fabcrowd/pokescan/design/output/cs2_motor_bracket.stl

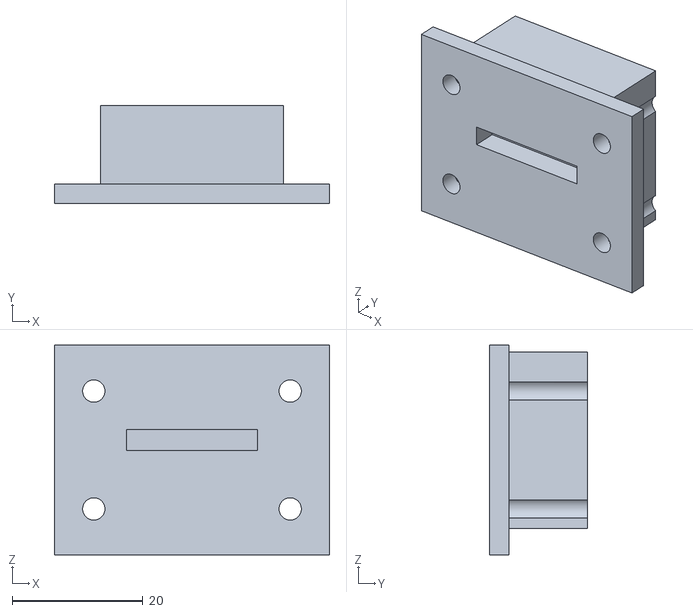
[picture p15: CAD file, 2026-06-29]
design/output/cs2_motor_bracket.stl
42.0 x 15.0 x 32.0
