fabcrowd/pokescan/design/output/cs2_separator_body.stl

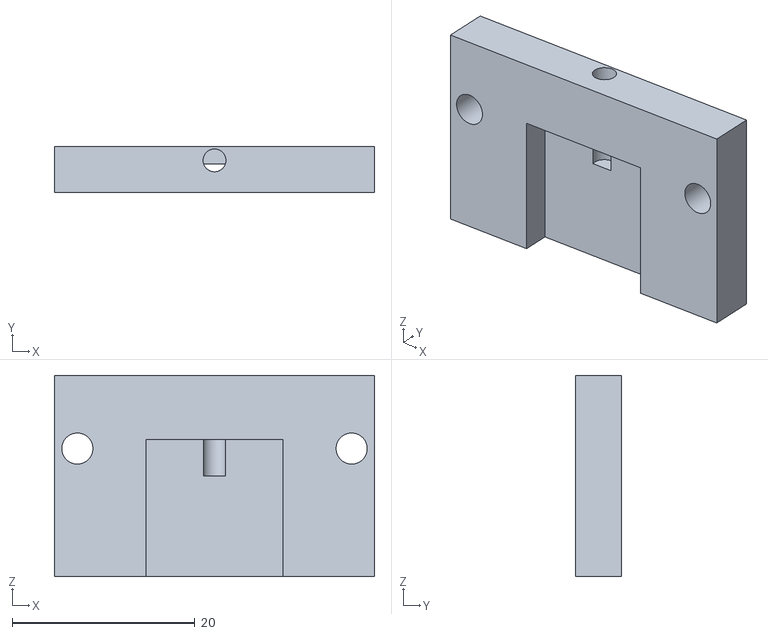
[picture p16: CAD file, 2026-06-29]
design/output/cs2_separator_body.stl
35.0 x 5.00 x 22.0
