fabcrowd/pokescan/design/output/cs2_rack_stand_fit_test.stl

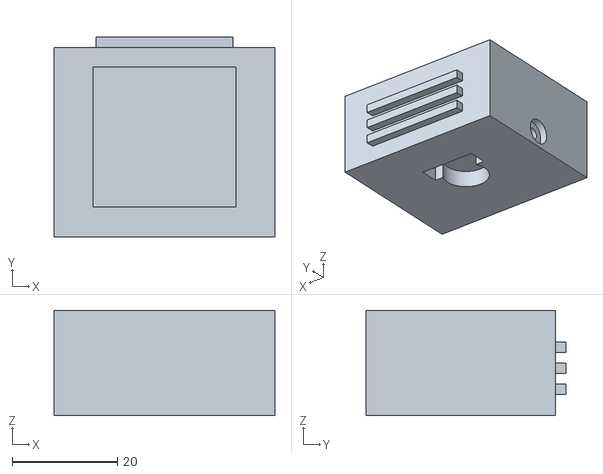
[picture p17: CAD file, 2026-06-29]
design/output/cs2_rack_stand_fit_test.stl
42.0 x 38.0 x 20.0
