fabcrowd/pokescan/design/output/cs2_push_rod.stl

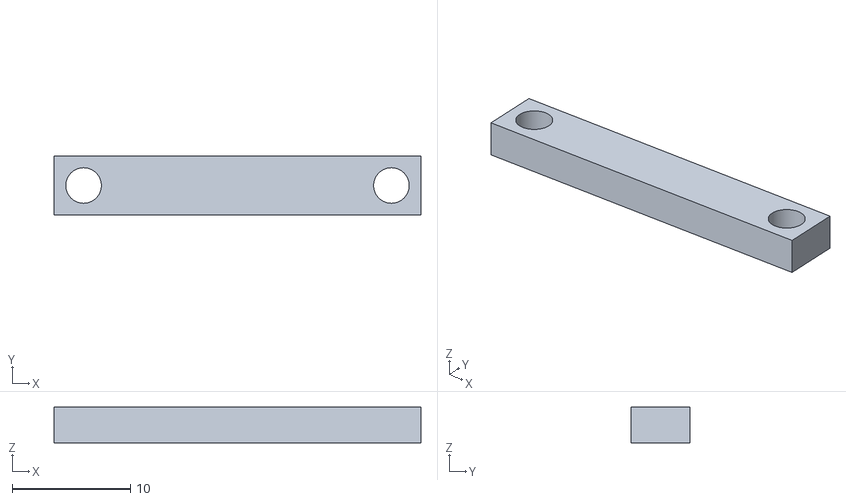
[picture p18: CAD file, 2026-06-29]
design/output/cs2_push_rod.stl
31.0 x 5.00 x 3.00
