fabcrowd/pokescan/design/output/cs2_roller_plate.stl

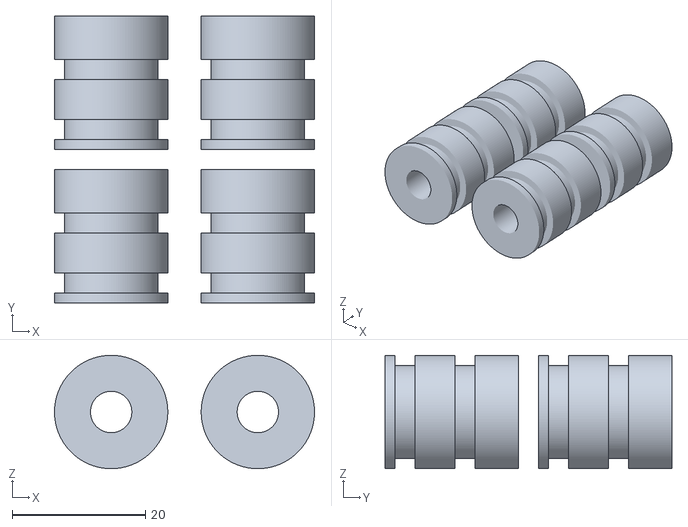
[picture p19: CAD file, 2026-06-29]
design/output/cs2_roller_plate.stl
39.0 x 43.0 x 17.0
