fabcrowd/pokescan/design/output/cs2_separator_gap_plate.stl

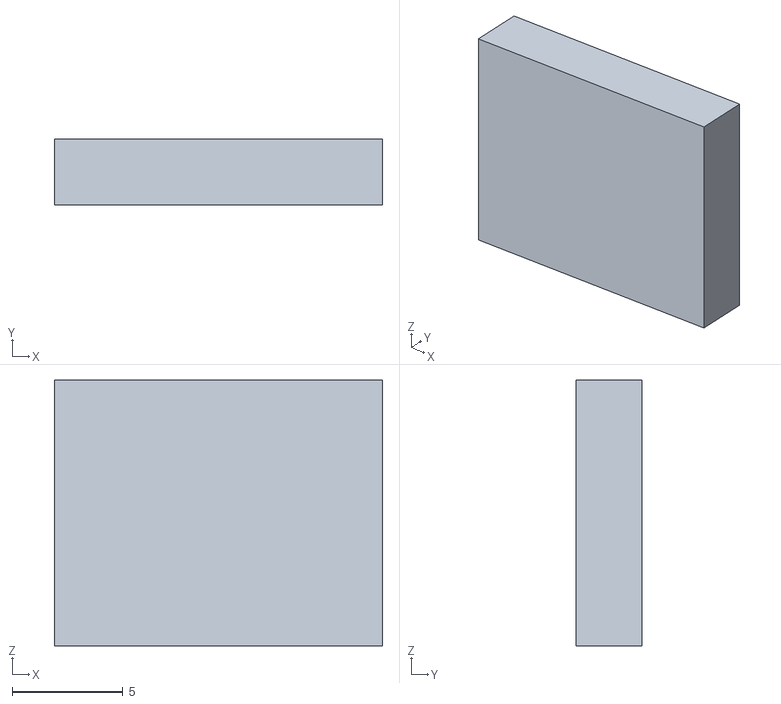
[picture p20: CAD file, 2026-06-29]
design/output/cs2_separator_gap_plate.stl
14.8 x 3.00 x 12.0
