fabcrowd/pokescan/design/output/cs2_roller.stl

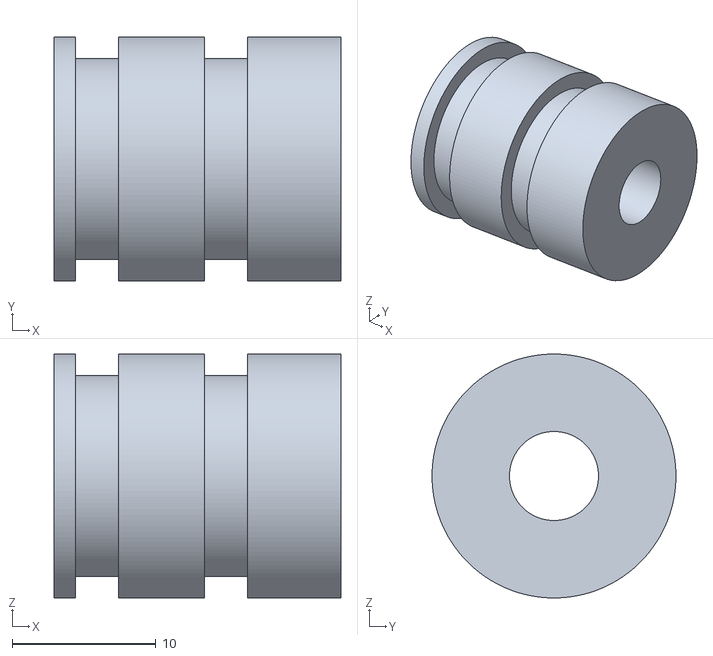
[picture p21: CAD file, 2026-06-29]
design/output/cs2_roller.stl
20.0 x 17.0 x 17.0
