fabcrowd/pokescan/design/output/cs2_rack_stand_platform.stl

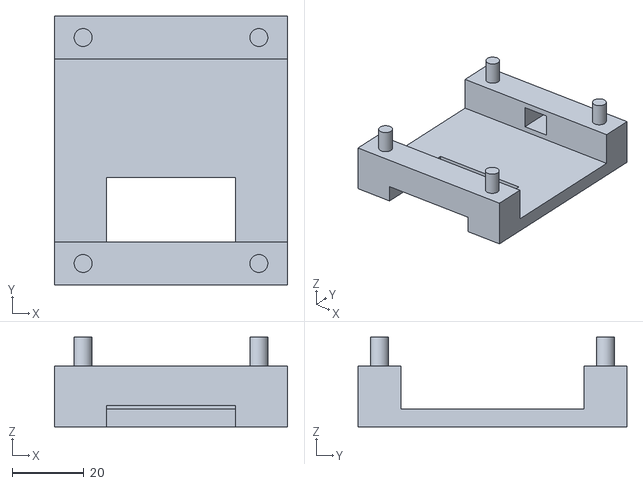
[picture p22: CAD file, 2026-06-29]
design/output/cs2_rack_stand_platform.stl
65.0 x 75.0 x 25.0
