fabcrowd/pokescan/design/output/cs2_wall_bot_left.stl

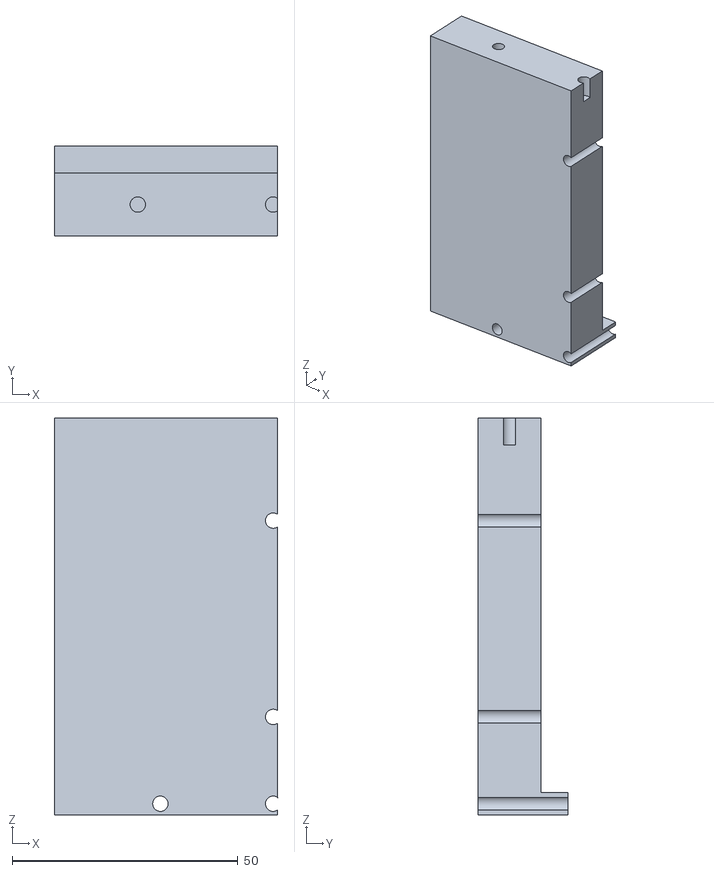
[picture p23: CAD file, 2026-06-29]
design/output/cs2_wall_bot_left.stl
49.5 x 20.0 x 88.0
